JVintera/HEX-LED-lamp/pracovni/Blynk web 1.PNG

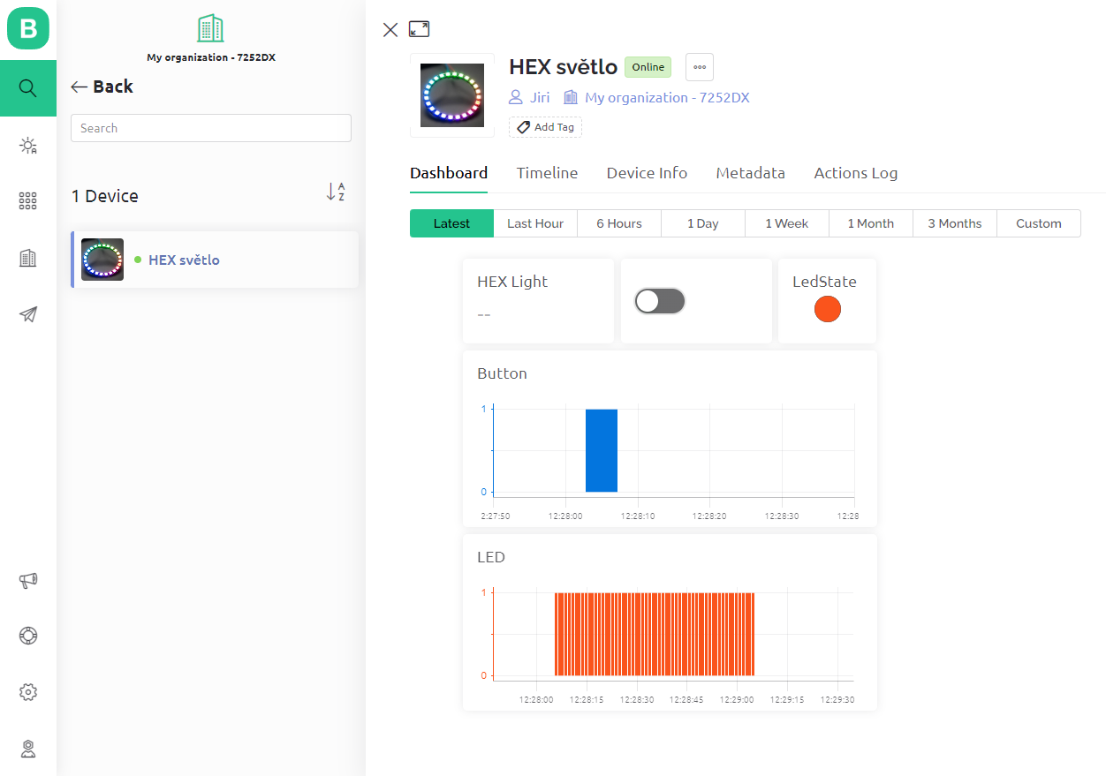
pracovni/Blynk web 1.PNG
