JVintera/HEX-LED-lamp/pracovni/Blynk web 4.PNG

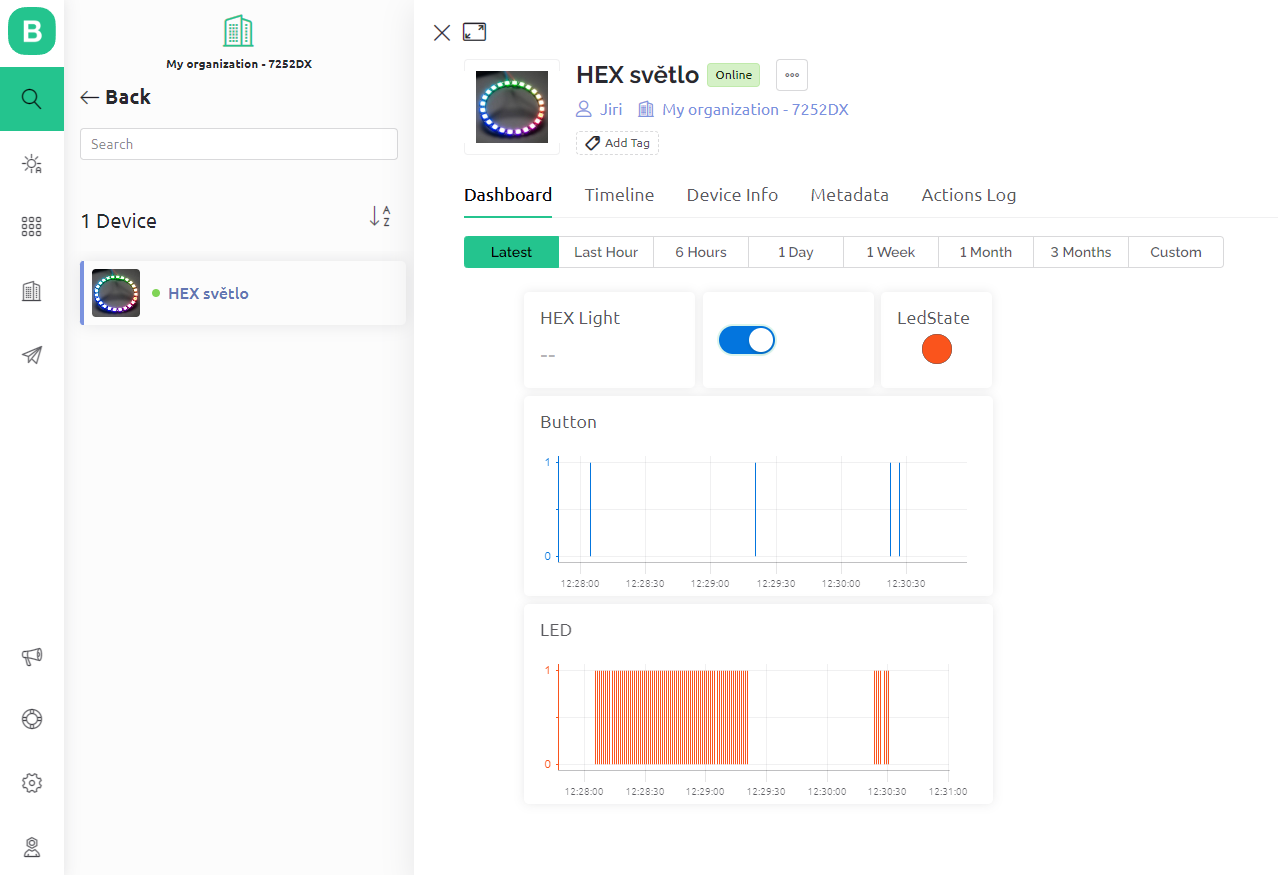
pracovni/Blynk web 4.PNG
