JVintera/HEX-LED-lamp/pracovni/IMG_20221026_002335683.jpg

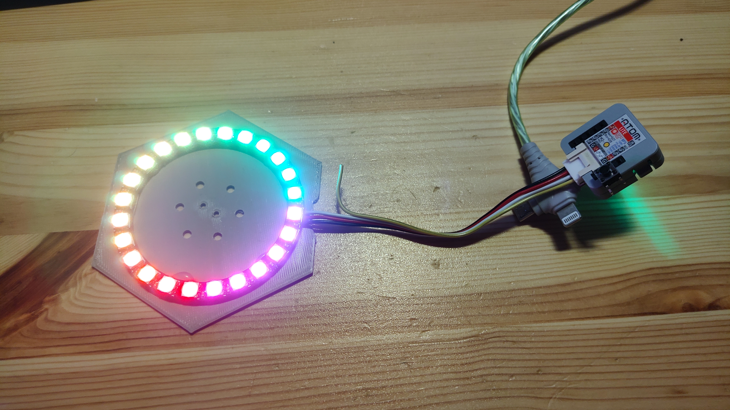
pracovni/IMG_20221026_002335683.jpg
