JVintera/HEX-LED-lamp/pracovni/IMG_20221026_003239249.jpg

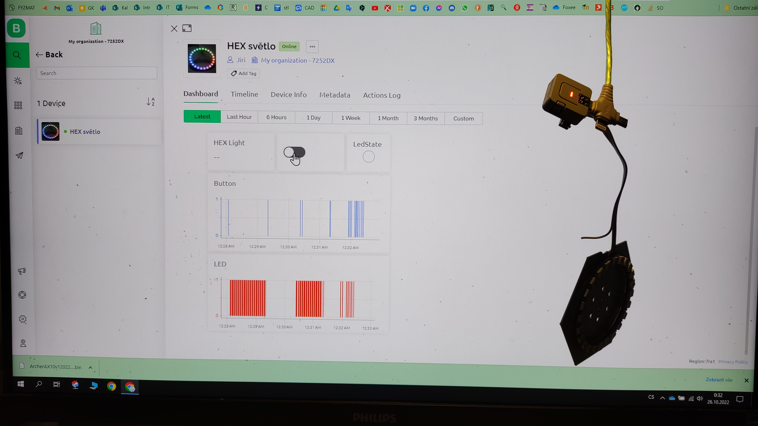
pracovni/IMG_20221026_003239249.jpg
