JVintera/HEX-LED-lamp/pracovni/IMG_20221026_003245765.jpg

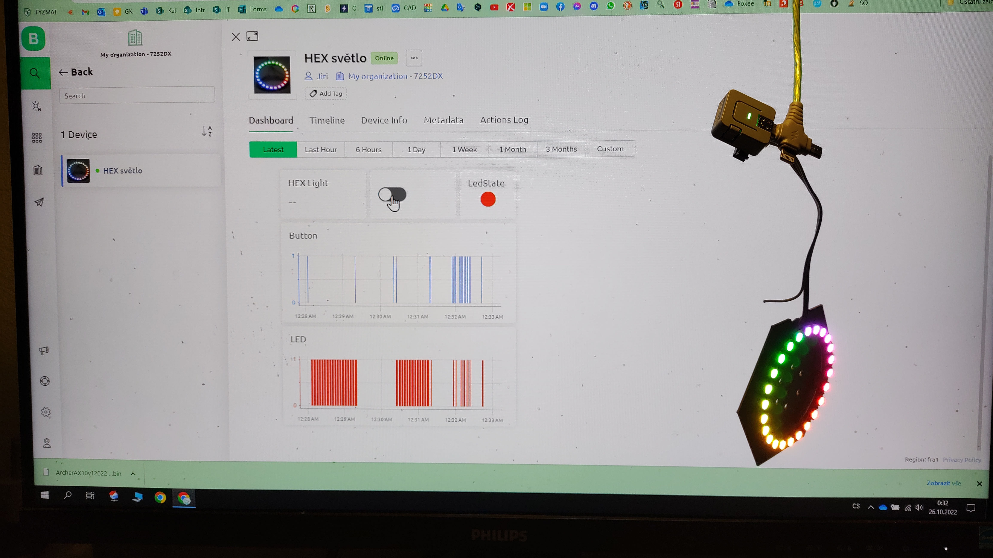
pracovni/IMG_20221026_003245765.jpg
