JVintera/HEX-LED-lamp/pracovni/IMG_20221026_003253168.jpg

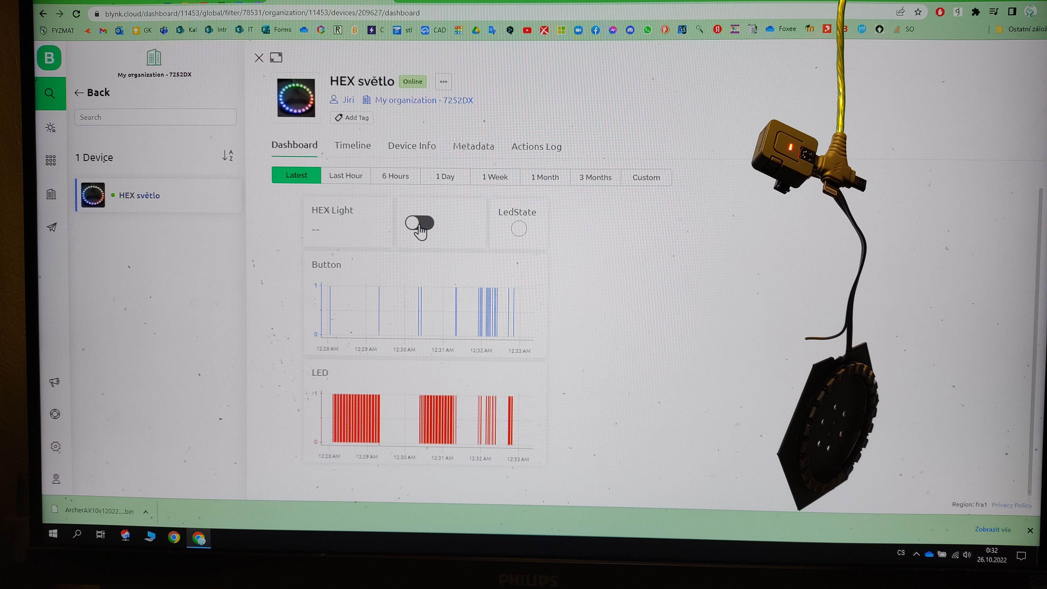
pracovni/IMG_20221026_003253168.jpg
