JVintera/HEX-LED-lamp/pracovni/Screenshot_20221026-003534.png

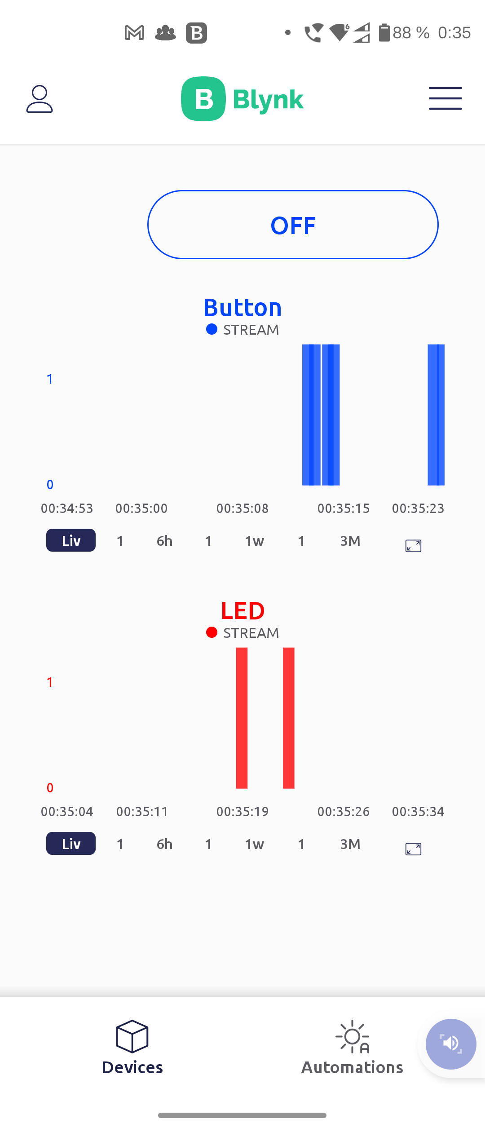
pracovni/Screenshot_20221026-003534.png
