JVintera/HEX-LED-lamp/pracovni/Screenshot_20221026-003549.png

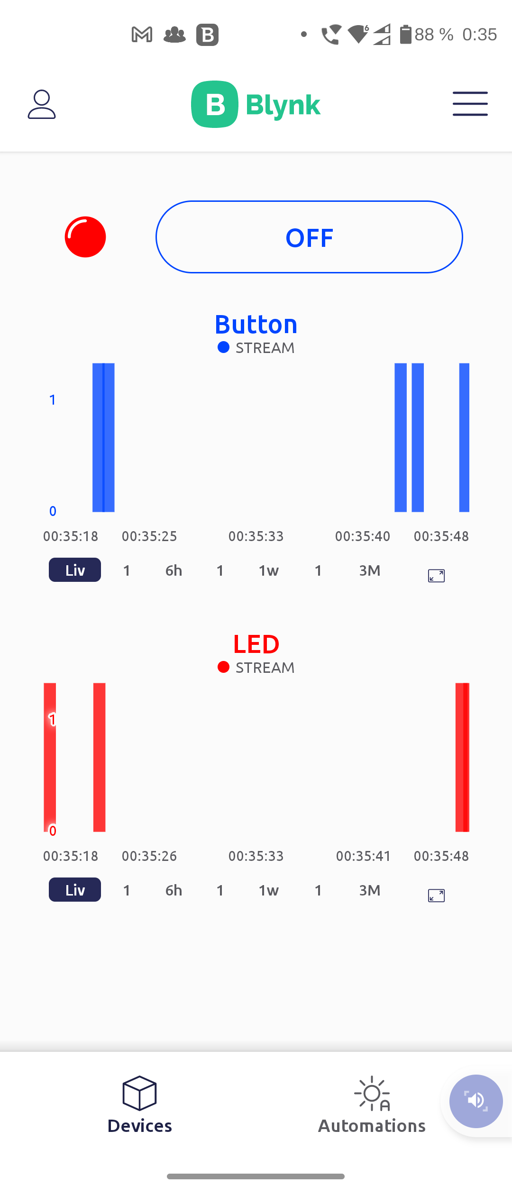
pracovni/Screenshot_20221026-003549.png
