JVintera/HEX-LED-lamp/pracovni/Screenshot_20221026-003632.png

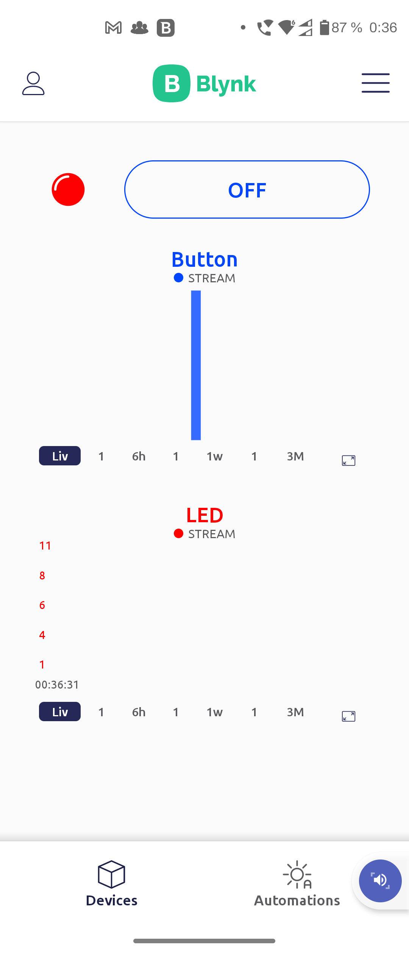
pracovni/Screenshot_20221026-003632.png
