JVintera/HEX-LED-lamp/WIFIlamp/v2/Obrázky/20230511_185647.jpg

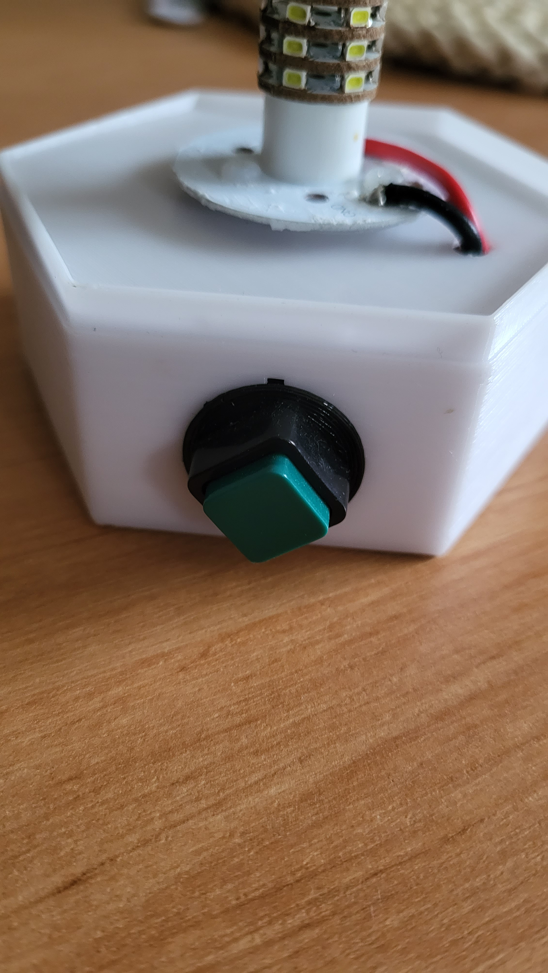
WIFIlamp/v2/Obrázky/20230511_185647.jpg
