JVintera/HEX-LED-lamp/RGBlamp/Schema/Zapojeni RGB lampicky/Zapojeni RGB lampicky.kicad_sch

## KiCad design RGBlamp/Schema/Zapojeni RGB lampicky/Zapojeni RGB lampicky.kicad_sch (2023-02-13, an earlier design)

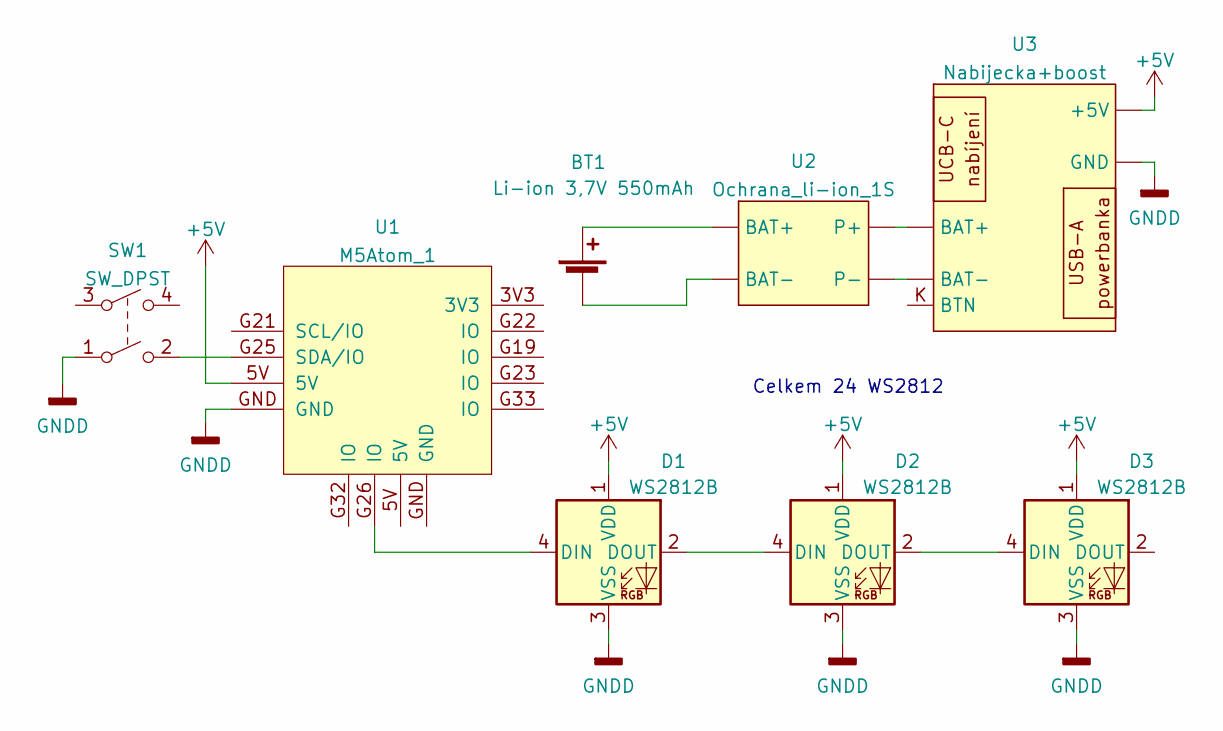
[picture p54: schematic Zapojeni RGB lampicky.kicad_sch]

Parts:
BT1: Li-ion 3,7V 550mAh
D1, D2, D3: WS2812B; LED_WS2812B_PLCC4_5.0x5.0mm_P3.2mm
SW1: SW_DPST
U1: M5Atom_1
U2: Ochrana_li-ion_1S
U3: Nabijecka+boost

Connections:
+5V: D1.1 (VDD), D2.1 (VDD), D3.1 (VDD), U1.5V, U3. (+5V)
GNDD: D1.3 (VSS), D2.3 (VSS), D3.3 (VSS), SW1.1, U1.GND, U3. (+5V)
unnamed: BT1.1 (+), U2.
unnamed: BT1.2 (-), U2.
unnamed: D1.2 (DOUT), D2.4 (DIN)
unnamed: D1.4 (DIN), U1.G26 (IO)
unnamed: D2.2 (DOUT), D3.4 (DIN)
unnamed: SW1.2, U1.G25 (SDA/IO)
unnamed: U2., U3. (+5V)

Notes on the sheet:
Celkem 24 WS2812
