JVintera/HEX-LED-lamp/LEDlamp/KiCAD/LEDlamp.kicad_sch

## KiCad design LEDlamp/KiCAD/LEDlamp.kicad_sch (2023-01-03)

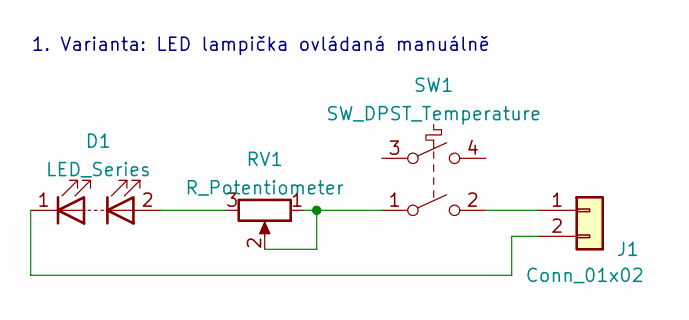
[picture p55: schematic LEDlamp.kicad_sch]

Parts:
D1: LED_Series
J1: Conn_01x02
RV1: R_Potentiometer
SW1: SW_DPST_Temperature

Connections:
unnamed: D1.1 (K), J1.2
unnamed: D1.2 (A), RV1.3
unnamed: J1.1, SW1.2
unnamed: RV1.1, RV1.2, SW1.1

Notes on the sheet:
1. Varianta: LED lampička ovládaná manuálně
