JVintera/HEX-LED-lamp/pracovni/HEX light WS2812/HEX light WS2812.kicad_sch

## KiCad design pracovni/HEX light WS2812/HEX light WS2812.kicad_sch (2023-02-04)

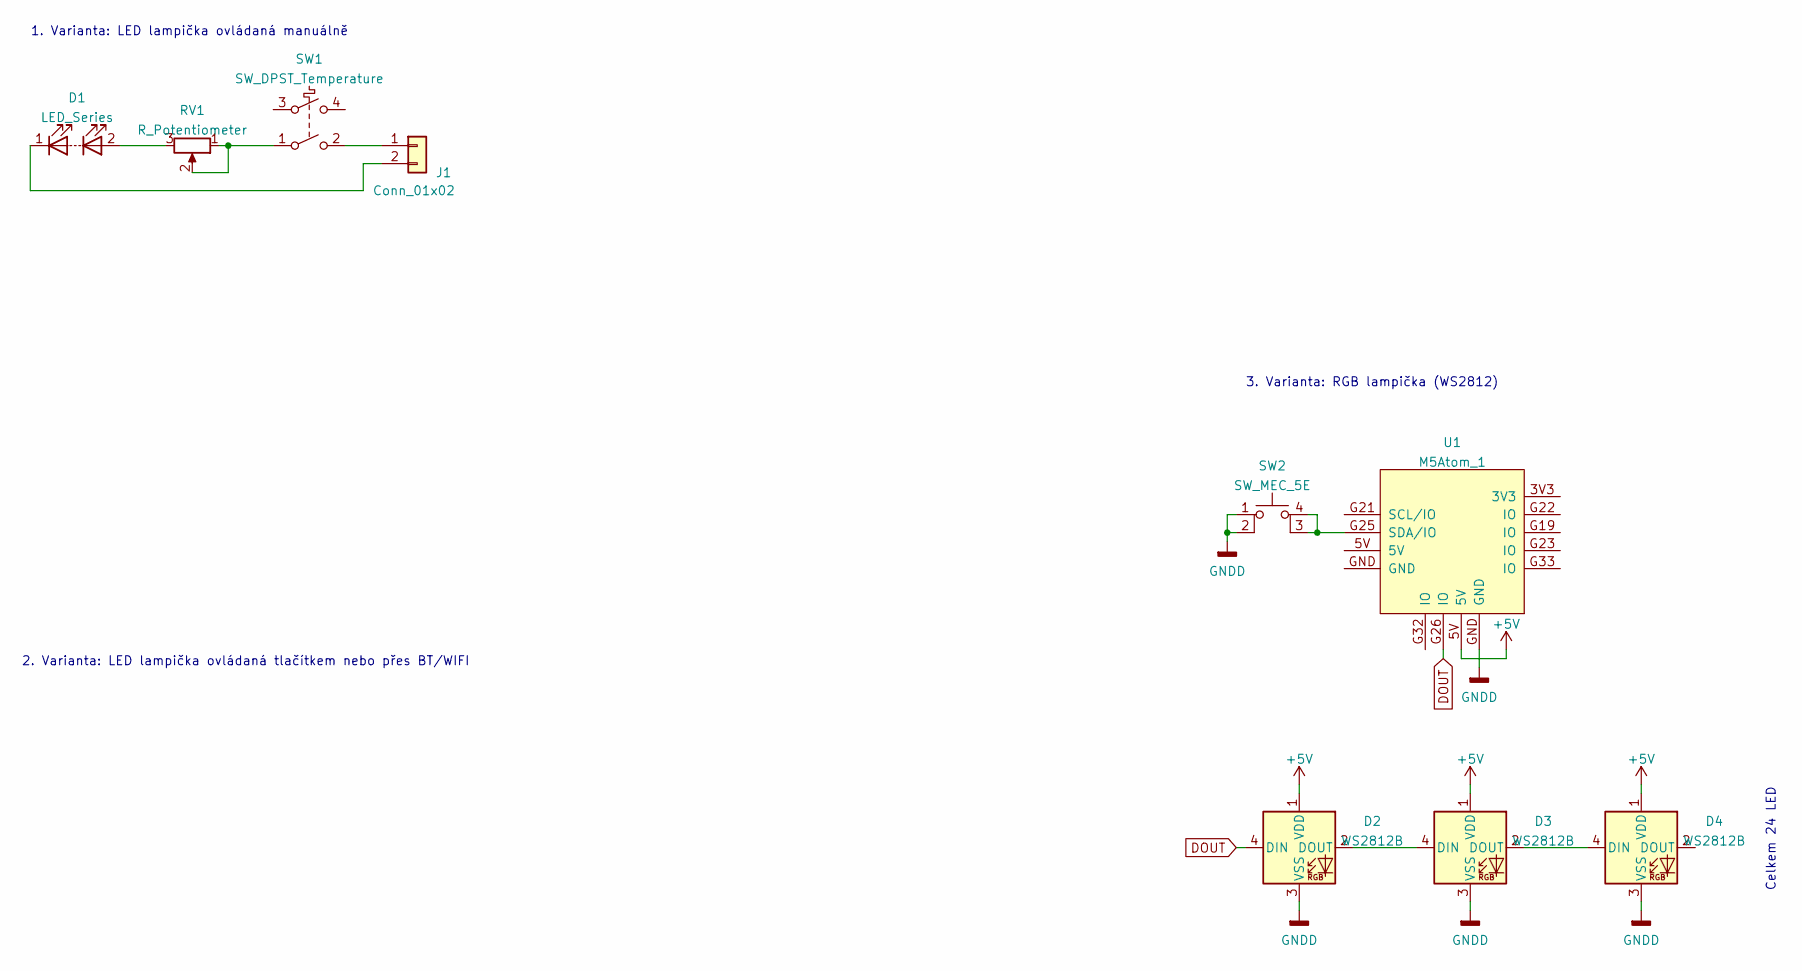
[picture p56: schematic HEX light WS2812.kicad_sch]

Parts:
D1: LED_Series
D2, D3, D4: WS2812B; LED_WS2812B_PLCC4_5.0x5.0mm_P3.2mm
J1: Conn_01x02
RV1: R_Potentiometer
SW1: SW_DPST_Temperature
SW2: SW_MEC_5E
U1: M5Atom_1

Connections:
+5V: D2.1 (VDD), D3.1 (VDD), D4.1 (VDD), U1.5V
DOUT: D2.4 (DIN), U1.G26 (IO)
GNDD: D2.3 (VSS), D3.3 (VSS), D4.3 (VSS), SW2.1, SW2.2, U1.GND
unnamed: D1.1 (K), J1.2
unnamed: D1.2 (A), RV1.3
unnamed: D2.2 (DOUT), D3.4 (DIN)
unnamed: D3.2 (DOUT), D4.4 (DIN)
unnamed: J1.1, SW1.2
unnamed: RV1.1, RV1.2, SW1.1
unnamed: SW2.3 (K), SW2.4 (A), U1.G25 (SDA/IO)

Notes on the sheet:
Celkem 24 LED
2. Varianta: LED lampička ovládaná tlačítkem nebo přes BT/WIFI
3. Varianta: RGB lampička (WS2812)
1. Varianta: LED lampička ovládaná manuálně
