JVintera/HEX-LED-lamp/RGBlamp/RGBlamp_v7-AdafruitIO/RGBlamp_v7.ino

// *** Co dodělat ***
// ????
// Ošetřit rozsvěcení LED když neni wifi
// Jak si to testuje wifi?
// Popsat v nápovědě soubor wifiConfig.h

//***************************************************
// Externí LED WB2812B přepínané tlačítkem a přes cloud
// Několik světelných efektů
//***************************************************
/*Zajímavé odkazy
  Adafruit IoT cloud
  Knihovny a příklady pro Adafruit IO cloud https://github.com/adafruit/Adafruit_IO_Arduino/blob/master/examples/adafruitio_14_neopixel/config.h
  Knihovna FastLED https://fastled.io/
  Návod https://learn.adafruit.com/adafruit-io-basics-digital-output/overview-2
*/

#include "setup.h"
